tihonov-e/MPPT_controller/Photo/IMG_20200429_210806.jpg

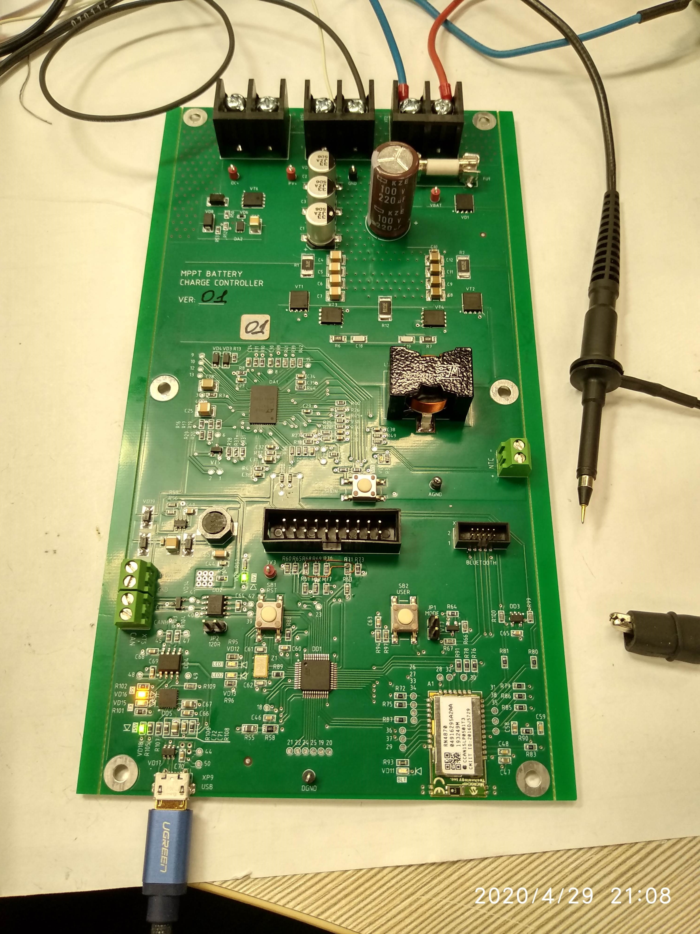
Photo/IMG_20200429_210806.jpg
