tihonov-e/MPPT_controller/HARDWARE (Altium)/Project Outputs for MPPT_controller/Архив/согласование_51066 (2 шт).xls

Пожалуйста, заполните перечень компонентов (спецификацию). Информация будет использоваться как для закупки комплектации, так и для монтажа. Перечень должен точно соответствовать файлам и монтажной схеме по позиционным обозначениям и содержать информацию, в том числе, о не устанавливаемых компонентах. |  |  |  |  |  |  |  |  | запрос 02665038
Комплектация указана для одного модуля. Закупку комплектующих произвести для 40 модулей.
Позиционное обозначение (RefDes)* | Наименование (PartNumber)* | Кол-во (Quantity)* | Номинал (Value)* | Тип корпуса (Package)* | Производитель (Manufacturer) | Описание (Description) | Возможная замена/примечание | № | Наименование | Производитель | Корпус | Прогноз
A1 | RN4870-I/RM128 | 1 |  | SMD Module | Microchip Technology | Bluetooth Module |  | 1 | RN4870-I/RM128 | MCRCH |  | на складе
C1, C2, C3 | EEH-ZA1J330P | 3 | 33mk | 8x8.3x10.5 mm Through Hole | Panasonic | EP-cap, 33mk, 63V, ±20% | 'EEH-ZA1J330P | 2 | EEHZA1J330P | PAN |  | 2 рабочих дня
C4, C5, C6, C7, C25, C40, C42 | 12101C225KAT2A | 7 | 2.2mk | 1210 | AVX | CAP CER, 2.2mk, X7R, ±10%, 100V, 1210 |  | 3 | 12101C225KAT2A | AVX | SMD 1210 [3.2x2.5mm] | на складе
C8, C9, C11, C12 | C4532X7S2A475M230KB | 4 | 4.7mk | 1812 | TDK | CAP CER, 4.7mk, X7S, ±20%, 100V, 1812 |  | 4 | GRM32DC72A475KE01L | MUR | SMD 1210 [3.2x2.5mm] | на складе | 100 В, 4.7 мкФ ±10%, X7S, SMD 1210 |  |  | СОГЛАСОВАТЬ!!!
C10, C26, C34, C38, C43, C44 | 06031C104KAT2A | 6 | 0.1mk | 0603 | AVX | CAP CER, 0.1mk, X7R, ±10%, 100V, 0603 |  | 5 | GRM188R72A104KA35D | MUR | SMD 0603 [1.6x0.8mm] | на складе | 100 В, 0.1 мкФ ±10%, X7R, SMD 0603 |  |  | СОГЛАСОВАТЬ!!!
C13 | EKZE101ELL221MK25S | 1 | 220mk | SMD; dia=12.5 x h=25 x step=5 mm | United Chemi-Con | CAP ALUM, 220mk, 100V, ±20% |  | 6 | EKZE101ELL221MK25S | UCC |  | 3 рабочих дня
C14, C17, C33, C35, C46, C48, C55, C59 | 06031C103KAT2A | 8 | 0.01mk | 0603 | AVX | CAP CER, 0.01mk, X7R, ±10%, 100V, 0603 |  | 7 | CL10B103KC8NNNC | SAMSUNG | SMD 0603 [1.6x0.8mm] | на складе | 100 В, 0.01 мкФ ±10%, X7R, SMD 0603, -55...125 °C |  |  | СОГЛАСОВАТЬ!!!
C15, C16 | GRM188R71C474KA88D | 2 | 0.47mk | 0603 | Murata | CAP CER, 0.47mk, X7R, ±10%, 16V, 0603 |  | 8 | GRM188R71C474KA88D | MUR | SMD 0603 [1.6x0.8mm] | на складе
C18, C19 | 12061A102KAT2A | 2 | 1000p | 1206 | AVX | CAP CER, 1000p, NP0, ±10%, 100V, 1206 |  | 9 | 12061A102JAT2A | AVX | SMD 1206 [3.2x1.6mm] | на складе
C20 | 0603YC102MAT4A | 1 | 1n | 0603 | AVX | CAP CER, 1n, X7R, ±20%, 16V, 0603 |  | 10 | CL10B102KA8NNNC | SAMSUNG | SMD 0603 [1.6x0.8mm] | на складе | 25 В, 1000 пФ ±10%, X7R, SMD 0603, -55...125 °C |  |  | СОГЛАСОВАТЬ!!!
C21, C22 | 0603YC332MAT4A | 2 | 3.3n | 0603 | AVX | CAP CER, 3.3n, X7R, ±20%, 16V, 0603 |  | 11 | CL10B332KB8NNNC | SAMSUNG | SMD 0603 [1.6x0.8mm] | на складе | 50 В, 3 300 пФ ±10%, X7R, SMD 0603, -55...125 °C |  |  | СОГЛАСОВАТЬ!!!
C23, C24 | 0603YD224KAT2A | 2 | 0.22mk | 0603 | AVX | CAP CER, 0.22mk, X5R, ±20%, 16V, 0603 |  | 12 | CL10B224KO8NNNC | SAMSUNG | SMD 0603 [1.6x0.8mm] | на складе | 16 В, 0.22 мкФ ±10%, X7R, SMD 0603, -55...125 °C |  |  | СОГЛАСОВАТЬ!!!
C27, C32, C50, C58 | 0603YC105KAT2A | 4 | 1mk | 0603 | AVX | CAP CER, 1mk, X7R, ±10%, 16V, 0603 |  | 13 | 0603YC105KAT2A | AVX | SMD 0603 [1.6x0.8mm] | на складе
C28 | 12101C105KAT2A | 1 | 1mk | 1210 | AVX | CAP CER, 1mk, X7R, ±10%, 100V, 1210 |  | 14 | 12101C105KAT2A | AVX | SMD 1210 [3.2x2.5mm] | на складе
C29, C30, C56 | 0603ZD225KAT2A | 3 | 2.2mk | 0603 | AVX | CAP CER, 2.2mk, X5R, ±10%, 10V, 0603 |  | 15 | 0603ZD225KAT2A | AVX | SMD 0603 [1.6x0.8mm] | 2 рабочих дня
C31, C67, C72 | 0805YC475KAT2A | 3 | 4.7mk | 0805 | AVX | CAP CER, 4.7mk, X7R, ±10%, 16V, 0805 |  | 16 | 0805YC475KAT2A | AVX | SMD 0805 [2.0x1.25mm] | на складе
C36 | 0603YC683KAT2A | 1 | 0.068mk | 0603 | AVX | CAP CER, 0.068mk, X7R, ±10%, 16V, 0603 |  | 17 | 0603YC683KAT2A | AVX | SMD 0603 [1.6x0.8mm] | 2 рабочих дня
C37 | 06033A221JAT2A | 1 | 220p | 0603 | AVX | CAP CER, 220p, X7R, ±5%, 25V, 0603 |  | 18 | 06033A221JAT2A | AVX | SMD 0603 [1.6x0.8mm] | 2 рабочих дня
C39 | 06035C682KAT2A | 1 | 6.8n | 0603 | AVX | CAP CER, 6.8n, X7R, ±10%, 50V, 0603 |  | 19 | CL10B682KB8NNNC | SAMSUNG | SMD 0603 [1.6x0.8mm] | на складе | 50 В, 6800 пФ ±10%, X7R, SMD 0603, -55...125 °C |  |  | СОГЛАСОВАТЬ!!!
C41 | 08051C104JAT2A | 1 | 0.1mk | 0805 | AVX | CAP CER, 0.1mk, X7R, ±10%, 100V, 0805 |  | 20 | C0805C104K1RACTU | KEM | SMD 0805 [2.0x1.25mm] | на складе | 100 В, 0.1 мкФ ±10%, X7R, SMD 0805, -55...125 °C |  |  | СОГЛАСОВАТЬ!!!
C45 | C3216X5R1E476M160AC | 1 | 47mk | 1206 | TDK | CAP CER, 47mk, X5R, ±10%, 25V, 1206 |  | 21 | C3216X5R1E476M160AC | TDK | SMD 1206 [3.2x1.6mm] | на складе
C47 | 0603ZD106MAT2A | 1 | 10mk | 0603 | AVX | CAP CER, 10mk, X5R, ±10%, 10V, 0603 |  | 22 | GRM188R61A106KE69D | MUR | SMD 0603 [1.6x0.8mm] | на складе | 10 В, 10 мкФ ±10%, X5R, SMD 0603 |  |  | СОГЛАСОВАТЬ!!!
C49, C51, C52, C53, C54, C57, C60, C63, C64, C65, C66, C68, C69, C70, C71 | 0603YC104KAT2A | 15 | 0.1mk | 0603 | AVX | CAP CER, 0.1mk, X7R, ±10%, 16V, 0603 |  | 23 | 0603YC104KAT2A | AVX | SMD 0603 [1.6x0.8mm] | на складе
C61, C62 | 06035A160JAT2A | 2 | 16p | 0603 | AVX | CAP CER, 16p, NP0, ±5%, 50V, 0603 |  | 24 | CC0603JRNPO9BN160 | YAG | SMD 0603 [1.6x0.8mm] | на складе
DA1 | LT8491EUKJ#PBF | 1 |  | 64-QFN (7x11) | Linear Technology | Charger IC Lead Acid 64-QFN (7x11) |  | 25 | LT8491EUKJ#PBF | AD |  | 11рабочих дней |  | дорогая позиция!!! СОГЛАСОВАТЬ!!!
DA2 | LTC4359CDCB | 1 |  | 6-DFN (2x3) | Linear Technology/Analog Devices | IC, Ideal Diode Controller, 6-DFN (2x3) |  | 26 | LTC4359CDCB#TRMPBF | AD |  | 8 рабочих дней
DA3 | LMR16006YDDCR | 1 |  | SOT23-6 | Texas Instruments | DC/DC buck converter, SOT23-6 |  | 27 | LMR16006XDDCT | TI | SOT23-6 | на складе |  | СОГЛАСОВАТЬ!!!
DA4 | MCP111T-195I/LB | 1 |  | SOT-23 | Microchip Technology | Supervisor,SOT-23 |  | 28 | MCP111T-195I/LB | MCRCH | SC-70-3 | 8 рабочих дней
DD1 | STM32F334C4T6 | 1 |  | 48-LQFP | STMicroelectronics | IC microcontroller, 32-Bit, Cortex-M4, 72MHz, 16KB, 12KB, 48-LQFP |  | 29 | STM32F334C4T6 | ST | LQFP-48 | 5 рабочих дней
DD2 | SN65HVD231DR | 1 |  | 8-SOIC | Texas Instruments | IC CAN transceiver, 8-SOIC |  | 30 | SN65HVD231D | TI | SOIC-8 | на складе
DD3 | 24CW1280T-I/OT | 1 |  | SOT-23-5 | Microchip Technology | EEPROM, 1KB (16Kx8), 400 kHz, I2C, SOT-23-5 |  | 31 | 24CW1280T-I/OT | MCRCH | SOT23-5 | 2 рабочих дня
DD4 | ISO7721DR | 1 |  | 8-SOIC | Texas Instruments | IC digital isolator, 8-SOIC |  | 32 | ADUM1201ARZ-RL7 | AD | SOIC-8 | на складе | СОГЛАСОВАТЬ!!!
DD5 | CP2102N-A02-GQFN24 | 1 |  | 24-QFN(4x4) | Silicon Labs | USB Bridge, USB to UART, USB2.0, 24-QFN(4x4) |  | 33 | CP2102N-A02-GQFN24R | SLAB | QFN-24 | 11 рабочих дней
FU1 | 01110506Z | 2 |  | Through Hole | Littelfuse | FUSE CLIP, 250VAC, 10A, 5x20mm |  | 34 | 01110506Z | LTL |  | 7 рабочих дней
 | 5HT 10-R | 1 | 10A | 5x20mm | Bel Fuse Inc. | FUSE CERAMIC 10A 250VAC 5X20MM | аналог 179021.10 SIBA //chipdip.ru | 35 | 0215010.MXP | LTL |  | на складе | СОГЛАСОВАТЬ!!!
JP1, JP2 | 61300411121 | 2 |  | PLS-2 Through Hole | Würth Elektronik | PLS-2 SINGLE ROW, 2pin, 2.54mm, 500VAC, 3A | аналог PLS-2 (DS1021-1x2) Сonnfly //chipdip.ru | 36 | 61300411121 | WURTH |  | 2 рабочих дня
L1 | см. переменные данные для исполнений |  |  |  |  |  |  |  |  | ПЕРЕМЕННЫЕ ДАННЫЕ
L2 | SRU8043-330Y | 1 | 33mkH | SMD Nonstandard | Bourns Inc. | Fixed inductor, 33mkH, ±15%, SMD Nonstandard, Ferrite, , 1.7A |  | 37 | SRU8043-330Y | BOURNS |  | 8 рабочих дней
L3 | LQM21DH100M70L | 1 | 10μH | 0805 | Murata Electronics | Fixed inductor, 10μH, ±20%, 0805, 250mA |  | 38 | LQM21DH100M70L | MUR |  | 8 рабочих дней
R1 | WSL25125L000FEA18 | 1 | 0.005 | 2512 | Vishay | Res, SMD, 0.005, ±1%, 2512, 2W |  | 39 | WSL25125L000FEA | VISHAY | SMD 2512 [6.4x3.2mm] | на складе
R2 | см. переменные данные для исполнений |  |  |  |  |  |  |  |  | ПЕРЕМЕННЫЕ ДАННЫЕ
R3, R4, R5, R14, R15 | CRCW060310R0JNEAC | 5 | 10 | 0603 | Vishay | Res, SMD, 10, ±5%, 0603, 0.1W |  | 40 | CR0603-JW-100ELF | BOURNS | SMD 0603 [1.6x0.8mm] | на складе | 0603 10 Ом ± 5% 200 ppm/K |  | СОГЛАСОВАТЬ!!!
R6, R7 | CRCW12061R20FKEA | 2 | 1.2 | 1206 | Vishay | Resistor film, 1.2, ±5%, 1206, 0.25W |  | 41 | CR-06FL7---1R2 | VIKING | SMD 1206 [3.2x1.6mm] | на складе | 1206 1.2 Ом ± 1% 200 ppm/K |  | СОГЛАСОВАТЬ!!!
R8, R9, R10, R11, R13 | CRCW06033R00JNEA | 5 | 3 | 0603 | Vishay | Res, SMD, 3, ±5%, 0603, 0.1W |  | 42 | CRCW06033R00JNEA | VISHAY | SMD 0603 [1.6x0.8mm] | 11 рабочих дней
R12 | см. переменные данные для исполнений |  |  |  |  |  |  |  |  | ПЕРЕМЕННЫЕ ДАННЫЕ
R16, R21, R40, R43, R54, R72, R75, R76, R78, R79, R80, R81, R83, R85, R86, R87, R91 | CRCW06030000Z0EA | 17 | 0 | 0603 | Vishay | Res, SMD, 0, ±1%, 0603, 0.1W |  | 43 | CRCW06030000Z0EA | VISHAY | SMD 0603 [1.6x0.8mm] | на складе
R17 | см. переменные данные для исполнений |  |  |  |  |  |  |  |  | ПЕРЕМЕННЫЕ ДАННЫЕ
R18, R89 | CRCW06031M00FKEA | 2 | 1M | 0603 | Vishay | Res, SMD, 1M, ±1%, 0603, 0.1W |  | 44 | CRCW06031M00FKEA | VISHAY | SMD 0603 [1.6x0.8mm] | на складе
R19 | CRCW0603196KFKEA | 1 | 196k | 0603 | Vishay | Res, SMD, 196k, ±1%, 0603, 0.1W |  | 45 | CRCW0603196KFKEA | VISHAY | SMD 0603 [1.6x0.8mm] | 5 рабочих дней
R20, R53, R64, R82, R90, R101, R102, R105, R108 | CRCW06031K00FKEA | 9 | 1k | 0603 | Vishay | Res, SMD, 1k, ±1%, 0603, 0.1W |  | 46 | CRCW06031K00FKEA | VISHAY | SMD 0603 [1.6x0.8mm] | на складе
R22 | CRCW060322K6FKEA | 1 | 22.6k | 0603 | Vishay | Res, SMD, 22.6k, ±1%, 0603, 0.1W |  | 47 | RC0603FR-0722K6L | YAG | SMD 0603 [1.6x0.8mm] | на складе | 0603 22.6 кОм ± 1% 100 ppm/K |  | СОГЛАСОВАТЬ!!!
R23 | CRCW0603115KFKEA | 1 | 115k | 0603 | Vishay | Res, SMD, 115k, ±1%, 0603, 0.1W |  | 48 | RC0603FR-07115KL | YAG | SMD 0603 [1.6x0.8mm] | на складе | 0603 115 кОм ± 1% 100 ppm/K |  | СОГЛАСОВАТЬ!!!
R24 | см. переменные данные для исполнений |  |  |  |  |  |  |  |  | ПЕРЕМЕННЫЕ ДАННЫЕ
R56 | CRCW060328K0FKEAHP | 1 | 28k | 0603 | Vishay | Res, SMD, 28k, ±1%, 0603, 0.1W |  | 49 | RC0603FR-0728KL | YAG | SMD 0603 [1.6x0.8mm] | на складе
R25 | см. переменные данные для исполнений |  |  |  |  |  |  |  |  | ПЕРЕМЕННЫЕ ДАННЫЕ
R26 | CRCW0603200KFKEAC | 1 | 200k | 0603 | Vishay | Res, SMD, 200k, ±1%, 0603, 0.1W |  | 50 | RC0603FR-07200KL | YAG | SMD 0603 [1.6x0.8mm] | на складе | 0603 200 кОм ± 1% 100 ppm/K |  | СОГЛАСОВАТЬ!!!
R27 | CRCW060320K0FKEC | 1 | 20k | 0603 | Vishay | Res, SMD, 20k, ±1%, 0603, 0.1W |  | 51 | CR-03FL7---20K | VIKING | SMD 0603 [1.6x0.8mm] | на складе | 0603 20 кОм ± 1% 100 ppm/K |  | СОГЛАСОВАТЬ!!!
R28 | CRCW06038K06FKEA | 1 | 8.06k | 0603 | Vishay | Res, SMD, 8.06k, ±1%, 0603, 0.1W |  | 52 | CRCW06038K06FKEA | VISHAY | SMD 0603 [1.6x0.8mm] | 5 рабочих дней
R29 | см. переменные данные для исполнений |  |  |  |  |  |  |  |  | ПЕРЕМЕННЫЕ ДАННЫЕ
R30, R50, R74, R88 | CRCW0603100KFKEA | 4 | 100k | 0603 | Vishay | Res, SMD, 100k, ±1%, 0603, 0.1W |  | 53 | CRCW0603100KFKEA | VISHAY | SMD 0603 [1.6x0.8mm] | на складе
R31 | CRCW06031K30FKEA | 1 | 1.3k | 0603 | Vishay | Res, SMD, 1.3k, ±1%, 0603, 0.1W |  | 54 | CR-03FL7---1K3 | VIKING | SMD 0603 [1.6x0.8mm] | на складе | 0603 1.3 кОм ± 1% 100 ppm/K |  | СОГЛАСОВАТЬ!!!
R32 | CRCW06031R00FKEAC | 1 | 1 | 0603 | Vishay | Res, SMD, 1, ±1%, 0603, 0.1W |  | 55 | RC0603FR-071RL | YAG | SMD 0603 [1.6x0.8mm] | на складе
R33 | CRCW0603549RFKEA | 1 | 549 | 0603 | Vishay | Res, SMD, 549, ±1%, 0603, 0.1W |  | 56 | CRCW0603549RFKEA | VISHAY | SMD 0603 [1.6x0.8mm] | 5 рабочих дней
R34 | CRCW060321K0FKEA | 1 | 21k | 0603 | Vishay | Res, SMD, 21k, ±1%, 0603, 0.1W |  | 57 | RC0603FR-0721KL | YAG | SMD 0603 [1.6x0.8mm] | на складе | 0603 21 кОм ± 1% 100 ppm/K |  | СОГЛАСОВАТЬ!!!
R35, R38, R39, R49, R60, R61, R62, R63, R66, R67, R77, R84, R92, R94, R97, R99, R100, R109 | CRCW060310K0JNEAC | 18 | 10k | 0603 | Vishay | Res, SMD, 10k, ±5%, 0603, 0.1W |  | 58 | RC0603JR-0710KL | YAG | SMD 0603 [1.6x0.8mm] | на складе
R36 | CRCW06033K01FKEA | 1 | 3.01k | 0603 | Vishay | Res, SMD, 3.01k, ±1%, 0603, 0.1W |  | 59 | RC0603FR-073K01L | YAG | SMD 0603 [1.6x0.8mm] | на складе | 0603 3.01 кОм ± 1% 100 ppm/K |  | СОГЛАСОВАТЬ!!!
R37*, R45* | не устанавливать |  |  | 0603 |  |  |  |  |  | ПЕРЕМЕННЫЕ ДАННЫЕ
R41 | CRCW0603215KFKEA | 1 | 215k | 0603 | Vishay | Res, SMD, 215k, ±1%, 0603, 0.1W |  | 60 | RC0603FR-07215KL | YAG | SMD 0603 [1.6x0.8mm] | на складе | 0603 215 кОм ± 1% 100 ppm/K |  | СОГЛАСОВАТЬ!!!
R42 | CRCW060353K6FKEA | 1 | 53.6k | 0603 | Vishay | Res, SMD, 53.6k, ±1%, 0603, 0.1W |  | 61 | RC0603FR-0753K6L | YAG | SMD 0603 [1.6x0.8mm] | на складе | 0603 53.6 кОм ± 1% 100 ppm/K |  | СОГЛАСОВАТЬ!!!
R44 | CRCW060325K5FKEA | 1 | 25.5k | 0603 | Vishay | Res, SMD, 25.5k, ±1%, 0603, 0.1W |  | 62 | CRCW060325K5FKEA | VISHAY | SMD 0603 [1.6x0.8mm] | 5 рабочих дней
R46 | CRCW060311K5FKEA | 1 | 11.5k | 0603 | Vishay | Res, SMD, 11.5k, ±1%, 0603, 0.1W |  | 63 | RC0603FR-0711K5L | YAG | SMD 0603 [1.6x0.8mm] | на складе | 0603 11.5 кОм ± 1% 100 ppm/K |  | СОГЛАСОВАТЬ!!!
R47 | CRCW06034K99FKEAC | 1 | 4.99k | 0603 | Vishay | Res, SMD, 4.99k, ±1%, 0603, 0.1W |  | 64 | RC0603FR-074K99L | VISHAY | SMD 0603 [1.6x0.8mm] | на складе | 0603 4.99 кОм ± 1% 100 ppm/K |  | СОГЛАСОВАТЬ!!!
R48 | CRCW0603110KFKEA | 1 | 110k | 0603 | Vishay | Res, SMD, 110k, ±1%, 0603, 0.1W |  | 65 | CR-03FL7--110K | VIKING | SMD 0603 [1.6x0.8mm] | на складе | 0603 110 кОм ± 1% 100 ppm/K |  | СОГЛАСОВАТЬ!!!
R51 | CRCW060335K7FKEA | 1 | 35.7k | 0603 | Vishay | Res, SMD, 35.7k, ±1%, 0603, 0.1W |  | 66 | CRCW060335K7FKEA | VISHAY | SMD 0603 [1.6x0.8mm] | 5 рабочих дней
R52 | CRCW060333K2FKEAC | 1 | 33.2k | 0603 | Vishay | Res, SMD, 33.2k, ±1%, 0603, 0.1W |  | 67 | RC0603FR-0733K2L | YAG | SMD 0603 [1.6x0.8mm] | на складе |  |  | СОГЛАСОВАТЬ!!!
R55 | B57401V2472J062 | 1 | 4.7k | 0805 | TDK | NTC resistor, 4k7, ±5%, 0805, 3650K, -55...+125°C |  | 68 | B57401V2472J062 | TDK-EPC | SMD 0805 [2.0x1.25mm] | 7 рабочих дней |  |  | СОГЛАСОВАТЬ!!!
R57, R93, R95, R96 | CRCW0603330RFKEAC | 4 | 330 | 0603 | Vishay | Res, SMD, 330, ±1%, 0603, 0.1W |  | 69 | CRCW0603330RFKEAC | VISHAY | SMD 0603 [1.6x0.8mm] | 11 рабочих дней |  |  | СОГЛАСОВАТЬ!!!
R58 | CRCW08055K10FKEA | 1 | 5.1k | 0805 | Vishay | Resistor film, 5.1k, ±1%, 0805, 0.125W |  | 70 | CRCW08055K10FKEA | VISHAY | SMD 0805 [2.0x1.25mm] | на складе
R59 | CRCW06038K45FKEA | 1 | 8.45k | 0603 | Vishay | Res, SMD, 8.45k, ±1%, 0603, 0.1W |  | 71 | RC0603FR-078K45L | YAG | SMD 0603 [1.6x0.8mm] | на складе | 0603 8.45 кОм ± 1% 100 ppm/K |  | СОГЛАСОВАТЬ!!!
R65, R68, R69, R70, R71, R73, R103, R104, R106, R107 | CRCW060322R0JNEA | 10 | 22 | 0603 | Vishay | Res, SMD, 22, ±5%, 0603, 0.1W |  | 72 | CR-03JL7---22R | VIKING | SMD 0603 [1.6x0.8mm] | на складе | 0603 22 Ом ± 5% 100 ppm/K |  | СОГЛАСОВАТЬ!!!
R98 | CRCW0805120RJNEA | 1 | 120 | 0805 | Vishay | Resistor film, 120, ±5%, 0805, 0.125W |  | 73 | CR-05JL7--120R | VIKING | SMD 0805 [2.0x1.25mm] | на складе | 0805 120 Ом ± 5% 100 ppm/K |  | СОГЛАСОВАТЬ!!!
SB1, SB2, SB3 | FSM2JSMAATR | 3 |  | 6x6mm | TE Connectivity | Tactile button, 6x6mm | аналог KLS7-TS6604-4.3-180 (IT-1102S) KLS //chipdip.ru | 74 | 2-1437565-9 | TE |  | 4 рабочих дней |  |  | СОГЛАСОВАТЬ!!!
VD1 | NTS10100MFST3G | 1 |  | 8-PowerTDFN, 5 Leads | ON Semiconductor | Schottky diode, 100V, 10A, 690mV @ 10A, 8-PowerTDFN, 5 Leads |  | 75 | NTS10100MFST3G | ONS | POWERSO-8 | 6 рабочих дней
VD2 | SMAJ48A-13-F | 1 |  | SMA | Diodes Incorporated | TVS DIODE UNI, 48V, 400W, SMA |  | 76 | SMAJ48A-TR | LTL | DO-214AC | на складе |  |  | СОГЛАСОВАТЬ!!!
VD3, VD4 | CMMR1U-02 TR | 2 |  | SOD-123F | Central Semi. | Ultra Fast Rectifier Single, 200V, 1A, SOD-123F |  | 77 | CMMR1U-02 TR | CSC | SOD123F | 8 рабочих дней |  |  | СОГЛАСОВАТЬ!!!
VD5, VD9, VD12, VD13, VD18 | 150060VS75000 | 5 |  | 0603 | Wurth | LED GREEN, 0603 |  | 78 | 150060VS75000 | WURTH | SMD 0603 [1.6x0.8mm] | 5 рабочих дней
VD6 | BZT52C12T-7 | 1 |  | SOD-523 | Diodes Incorporated | Zener diode, 12V, 300mW, SOD-523 |  | 79 | BZT52C12T-7 | DIODES | SOD523 | 8 рабочих дней
VD7 | SMAT70A-13-F | 1 |  | SMA | Diodes Incorporated | TVS DIODE UNI, 70V, 400W, SMA |  | 80 | SMAT70A-13-F | DIODES | DO-214AC | 6 рабочих дней
VD8 | SMAJ24A-13-F | 1 |  | SMA | Diodes Incorporated | TVS DIODE UNI, 24V, 400W, SMA |  | 81 | SMAJ24A | LTL | DO-214AC | на складе |  |  | СОГЛАСОВАТЬ!!!
VD10, VD19, VD20 | MBR0580S1-7 | 3 |  | SMA | Vishay | Schottky diode, 100V, 1A, , SMA |  | 82 | MBR0580S1-7 | DIODES | SOD123 | на складе |  |  | СОГЛАСОВАТЬ!!!
VD11, VD15 | 150060BS75000 | 2 |  | 0603 | Wurth | LED, 0603 BLUE |  | 83 | 150060BS75000 | WURTH | SMD 0603 [1.6x0.8mm] | 8 рабочих дней |  |  | СОГЛАСОВАТЬ!!!
VD14 | ESDCAN06-2BLY | 1 |  | SOT-23 | STMicroelectronics | TVS diode, 24V, 230W peak, 3A, 13pF, SOT-23, -40...+150°C |  | 84 | ESDCAN06-2BLY | ST |  | 11 рабочих дней |  |  | СОГЛАСОВАТЬ!!!
VD16 | 150060YS75000 | 1 |  | 0603 | Wurth | LED, 0603 YELLOW |  | 85 | KP-1608SYCK | KGB | LED 0603 [1608 metric] | на складе |  |  | СОГЛАСОВАТЬ!!!
VD17 | USBLC6-2SC6 | 1 |  | SOT23-6L | ST Microelectronics | TVS USB ESD, 5V, SOT23-6L |  | 86 | USBLC6-2SC6 | ST | SOT23-6 | на складе
VT1, VT2, VT3, VT4 | BSC110N15NS5 | 4 |  | PG-TDSON-8 | Infineon Technologies | MOSFET N-ch, 150V, PG-TDSON-8 |  | 87 | BSC110N15NS5ATMA1 | INFIN | PG-TDSON-8 | 5 рабочих дней |  |  | СОГЛАСОВАТЬ!!!
VT5, VT7, VT8 | MMBT3904-7-F | 3 |  | SOT-23 | Diodes Inc. | NPN transistor, 40V, 200mA, SOT-23 |  | 88 | MMBT3904LT1G | ONS | SOT23 | на складе |  |  | СОГЛАСОВАТЬ!!!
VT6 | FDMS86101 | 1 |  | 8-PowerTDFN | ON Semiconductor | MOSFET N-ch, 100V, 12A, 8-PowerTDFN |  | 89 | FDMS86101 | ONS-FAIR | TDFN-8 | 6 рабочих дней
XP1 | 5000 | 1 |  | Through Hole | Keystone | Test Point, Red |  | 90 | 5000 | KEYS |  | на складе
XP2 | 5000 | 1 |  | Through Hole | Keystone | Test Point, Red |  | 91 | 5000 | KEYS |  | на складе
XP3 | 5000 | 1 |  | Through Hole | Keystone | Test Point, Red |  | 92 | 5000 | KEYS |  | на складе
XP4 | 5001 | 1 |  | Through Hole | Keystone | Test Point, Black |  | 93 | 5001 | KEYS |  | 2 рабочих дня
XP5 | 5001 | 1 |  | Through Hole | Keystone | Test Point, Black |  | 94 | 5001 | KEYS |  | 2 рабочих дня
XP6 | 5000 | 1 |  | Through Hole | Keystone | Test Point, Red |  | 95 | 5000 | KEYS |  | на складе
XP7 | IDC-20M | 1 |  | IDC2.54-20 Through Hole | On Shore Technology Inc. | Connector IDC, 20pin, 2.54mm | аналог BH-20 (DS1013-20S) Сonnfly //chipdip.ru | 96 | IDC-20M | KLS |  | на складе
XP8 | 3220-10-0300-00 | 1 |  | IDC1.27-10 SMD | CNC Tech | IDC1.27-10M (SMD), 10pin, 1.27mm, , 1A |  | 97 | 3220-10-0300-00 | CNC TECH |  | 3 рабочих дня
 | 3230-10-0101-00 | 1 |  | кабельная часть (ответка) | CNC Tech | CONN SOCKET 10POS IDC GOLD |  | 98 | 3230-10-0101-00 | CNC TECH |  | 2 рабочих дня
XP9 | 0475890001 | 1 |  | SMD Nonstandard | Molex | USB micro (AB) |  | 99 | 47589-0001 | MOL |  | на складе
XP10 | 5001 | 1 |  | Through Hole | Keystone | Test Point, Black |  | 100 | 5001 | KEYS |  | 2 рабочих дня
XT1, XT2, XT4, XT6 | 6PCV-02-006 | 3 |  | Through Hole | TE Connectivity | Connector, 2pin, 9.53mm, 300VAC, 25A |  | 101 | 6PCV-02-006 | TE |  | 11 рабочих дней |  |  | СОГЛАСОВАТЬ!!!
XT3, XT5, XT6 | 0393570002 | 3 |  | Through Hole | Molex | TERM CONN., 3pin, 3.5mm | китайский аналог DG350-3.5-02P-14 Degson //chipdip.ru | 102 | 1546551-2 | TE |  | 11 рабочих дней |  |  | СОГЛАСОВАТЬ!!!
Z1 | ECS-80-18-30B-AGN-TR | 1 |  | case 5032, 4-SMD (5.00mm x 3.20mm) | ECS Inc. | Oscilator, 8MHz, 18pF, ±25ppm, case 5032 |  | 103 | ECS-80-18-30B-AGN-TR | ECS |  | 11 рабочих дней
 | Переменные данные для исполнений
 | -00
L1 | 7443633300 | 1 | 33mkH | SMD Shielded | Würth Elektronik | Fixed inductor, 33mkH, ±15%, SMD Shielded, Ferrite (MnZn), , 12A |  | 104 | 7443633300 | WURTH |  | 2 рабочих дня
R2 | WSL2512R0250FEA18 | 1 | 0.025 | 2512 | Vishay | Res, SMD, 0.025, ±1%, 2512, 2W |  | 105 | CRA2512-FZ-R025ELF | BOURNS |  | на складе |  |  | СОГЛАСОВАТЬ!!!
R12 | WSL25126L000FEA18 | 1 | 0.006 | 2512 | Vishay | Res, SMD, 0.006, ±1%, 2512, 2W |  | 106 | WSL25126L000FEA18 | VISHAY | SMD 2512 [6.4x3.2mm] | 7 рабочих дней
R17 | CRCW060391K0FKEA | 1 | 91k | 0603 | Vishay | Res, SMD, 91k, ±1%, 0603, 0.1W |  | 107 | RC0603FR-0791KL | YAG | SMD 0603 [1.6x0.8mm] | на складе | 0603 91 кОм ± 1% 100 ppm/K |  | СОГЛАСОВАТЬ!!!
R24 | CRCW060328K0FKEAHP | 2 | 28k | 0603 | Vishay | Res, SMD, 28k, ±1%, 0603, 0.1W |  | 108 | RC0603FR-0728KL | YAG | SMD 0603 [1.6x0.8mm] | на складе | 0603 28 кОм ± 1% 100 ppm/K |  | СОГЛАСОВАТЬ!!!
R25 | CRCW06035K60FKEA | 1 | 5.6k | 0603 | Vishay | Res, SMD, 5.6k, ±1%, 0603, 0.1W |  | 109 | CR-03FL7---5K6 | VIKING | SMD 0603 [1.6x0.8mm] | на складе | 0603 5.6 кОм ± 1% 100 ppm/K |  | СОГЛАСОВАТЬ!!!
R29 | CRCW060311K3FKEA | 1 | 11.3k | 0603 | Vishay | Res, SMD, 11.3k, ±1%, 0603, 0.1W |  | 110 | RC0603FR-0711K3L | YAG | SMD 0603 [1.6x0.8mm] | на складе | 0603 11.3 кОм ± 1% 100 ppm/K |  | СОГЛАСОВАТЬ!!!
 | -01
L1 | 7443632200 | 1 | 22mkH | SMD Shielded | Würth Elektronik | Fixed inductor, 22mkH, ±15%, SMD Shielded, Ferrite (MnZn), , 12A |  | 111 | 7443632200 | WURTH |  | 6 рабочих дней
R2 | WSL2512R0120FEA18 | 1 | 0.012 | 2512 | Vishay | Res, SMD, 0.012, ±1%, 2512, 2W |  | 112 | WSL2512R0120FEA18 | VISHAY | SMD 2512 [6.4x3.2mm] | 7 рабочих дней
R12 | WSL2512R0150FEA18 | 1 | 0.015 | 2512 | Vishay | Res, SMD, 0.015, ±1%, 2512, 2W |  | 113 | WSL2512R0150FEA | VISHAY | SMD 2512 [6.4x3.2mm] | на складе |  |  | СОГЛАСОВАТЬ!!!
R17 | RT0603BRD0794K2L | 1 | 94.2k | 0603 | Yageo | Res, SMD, 94.2k, ±0.1%, 0603, 0.1W |  | 114 | RT0603BRD0794K2L | YAG | SMD 0603 [1.6x0.8mm] | 11 рабочих дней
R24 | CRCW060314K3FKEA | 1 | 14.3k | 0603 | Vishay | Res, SMD, 14.3k, ±1%, 0603, 0.1W |  | 115 | RC0603FR-0714K3L | YAG | SMD 0603 [1.6x0.8mm] | на складе
R25 | CRCW06032K87FKEA | 1 | 2.87k | 0603 | Vishay | Res, SMD, 2.87k, ±1%, 0603, 0.1W |  | 116 | RC0603FR-072K87L | YAG | SMD 0603 [1.6x0.8mm] | на складе
R29 | CRCW06037K32FKEA | 1 | 7.32k | 0603 | Vishay | Res, SMD, 7.32k, ±1%, 0603, 0.1W |  | 117 | RC0603FR-077K32L | YAG | SMD 0603 [1.6x0.8mm] | на складе | 0603 7.32 кОм ± 1% 100 ppm/K |  | СОГЛАСОВАТЬ!!!
 | Дополнительные комплектующие для настройки модулей
 | кол-во указано на все модули
 | (купить, но не устанавливать)
Позиционное обозначение (RefDes)* | Наименование (PartNumber)* | Кол-во (Quantity)* | Номинал (Value)* | Тип корпуса (Package)* | Производитель (Manufacturer) | Описание (Description) | Возможная замена/примечание
- | 7443631000 | 2 | - | SMD Shielded | Würth Elektronik | Fixed inductor, 10mkH, ±15%, SMD Shielded, Ferrite (MnZn), , 16A | - | 118 | 7443631000 | WURTH |  | 5 рабочих дней
- | 7443631500 | 2 | - | SMD Shielded | Würth Elektronik | Fixed inductor, 15mkH, ±15%, SMD Shielded, Ferrite (MnZn), , 14A | - | 119 | 7443631500 | WURTH |  | 5 рабочих дней
- | 7443634700 | 2 | - | SMD Shielded | Würth Elektronik | Fixed inductor, 47mkH, ±15%, SMD Shielded, Ferrite (MnZn), , 12A | - | 120 | 7443634700 | WURTH |  | 2 рабочих дня
- | QPC02SXGN-RC | 50 | - | jumper | Sullins Connector Solutions | CONN JUMPER SHORTING .100" GOLD | - | 121 | MJ-O-6 | CONNFLY |  | на складе | DS1027-2ABN0 |  | СОГЛАСОВАТЬ!!!
Примечание:
1) поля, обозначенные *, обязательны для заполнения 2) для пассивных компонентов (резисторов, конденсаторов, индуктивностей) допускается приводить перечень основных параметров в поле "Наименование (PartNumber)". Например: "0603 0,1 Вт 49,9 Ом ±1%" или "1206 X5R - 25 В - 1 мкФ ±10%"
