tihonov-e/MPPT_controller/HARDWARE (Altium)/Project Outputs for MPPT_controller/Архив/BOM_service_tools.xls

Designator | PartNumber | Manufacturer | Quantity | Comment | HelpURL
- | Отладчик ST-LINK/V2-ISOL | STMicroelectronics | 1 | DEBUGGER/PROGRAMMER STM8/32 | https://www.chipdip.ru/product/st-link-v2-isol?from=suggest_product https://spb.terraelectronica.ru/product/1107586
- | USB-CAN модуль 3204001-01 | SysTec | 1 | USB-CAN модуль | http://www.simecs.ru/catalog/sys-tec/interfeysy-i-shlyuzy-can-pc-galvanicheskaya-razvyazka/3204001/
 | Сетевой адаптер Bluetooth USB-BT400 USB 2.0 | ASUS | 1 | USB-Bluetooth 4.0 | https://www.citilink.ru/catalog/computers_and_notebooks/net_equipment/netcards/858952/
- | G218C, Корпус для РЭА | Gainta Industries | 3 | 222х146х55 мм, пластик, с прозрачной крышкой | https://www.chipdip.ru/product/g218c
- | Стойка PCHSN-15 (6mm) | Ningbo connfly electronic | 30 | Стойка для п/плат,шестигр., латунь, М3, 15мм, никелированные | https://www.chipdip.ru/product/pchsn-15-2?from=rec_product
- | Гайка оцинк. М3 | ООО "Крепежные системы" | 2 уп. | Mb0700003-P3, Гайка оцинк. М3 DIN934 уп. - 32 шт. (фасов.) | https://www.chipdip.ru/product/mb0700003-p3
- | Шайба M3 | Россия | 2 уп. | Шайба изолирующая под М3.0 (50шт.) стеклотекстолит, толщина 0.5мм. внешний диаметр 7мм | https://www.chipdip.ru/product0/9000016482
