tihonov-e/MPPT_controller/Issue_List/Список новых компонентов.xlsx

Здесь приведены новые компоненты для MPPT контроллера -01 исполнения
По результатам наладки
01 исполнение будет универсальным для всех панелей
Тихонов Е.Н. 18.05.2020
Для изготовления одной платы понадобятся:
Позиционное обозначение (RefDes)* | Наименование (PartNumber)* | Кол-во (Quantity)* | Номинал (Value)* | Тип корпуса (Package)* | Производитель (Manufacturer) | Описание (Description) | Возможная замена/примечание | Ссылка поставщика (HelpURL)
DD1 | STM32F334C8T6 | 1 |  | 48-LQFP | STMicroelectronics | IC microcontroller, 32-Bit, Cortex-M4, 72MHz, 64KB, 12KB, 48-LQFP | есть в наличии 5 шт. | https://www.electronshik.ru/item/ST/STM32F334C8T6
VT1 - VT4 | BSC060N10NS3 G | 4 |  |  | Infenion | 100V | BSC070N10NS3 G (Rds больше на 1 мОм, но это не критично.) | https://www.chipdip.ru/product0/8001780089 https://www.chipdip.ru/product1/8002079021
R12 | CRA2512-FZ-R010ELF | 1 | 10 мОм | 2512 | Bourns | 2 Вт, 1% |  | https://www.electronshik.ru/item/BOURNS/CRA2512-FZ-R010ELF
R18 | RC0603FR-07820KL | 1 | 820k | 0603 | YAGEO | 1% |  | https://www.electronshik.ru/item/YAG/RC0603FR-07820KL
R22 | RC0603FR-0724KL | 1 | 24k | 0603 | YAGEO | 1% |  | https://www.electronshik.ru/item/YAG/RC0603FR-0724KL
R23 | RC0603FR-07120KL | 1 | 120k | 0603 | YAGEO | 1% |  | https://www.electronshik.ru/item/YAG/RC0603FR-07120KL
R17 | RC0603FR-07107KL |  | 107k | 0603 | YAGEO | 1% |  | https://www.electronshik.ru/item/YAG/RC0603FR-07107KL
R20 | RC0603FR-070RL | 1 | 0 | 0603 | YAGEO | 1% |  | https://www.electronshik.ru/item/YAG/RC0603FR-070RL
R24 | RC0603FR-078K66L | 1 | 8.66k | 0603 | YAGEO | 1% |  | https://www.electronshik.ru/item/YAG/RC0603FR-078K66L
R29 | RC0603FR-074K87L | 1 | 4.87k | 0603 | YAGEO | 1% |  | https://www.electronshik.ru/item/YAG/RC0603FR-074K87L
R25 | RC0603FR-071K69L | 1 | 1.69k | 0603 | YAGEO | 1% |  | https://www.electronshik.ru/item/YAG/RC0603FR-071K69L
